shawnchain/aprs/doc/wiki/H618B_HOWTO/H618B.JPG

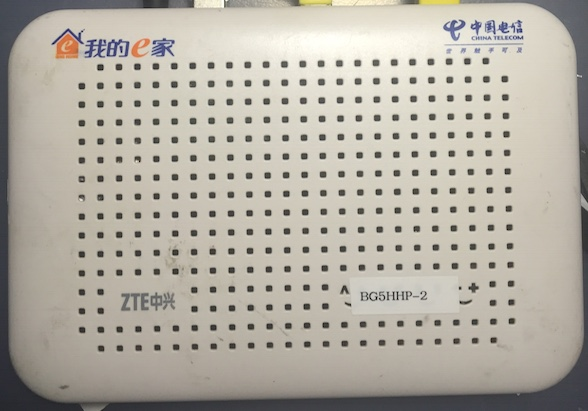
doc/wiki/H618B_HOWTO/H618B.JPG
