shawnchain/aprs/doc/wiki/H618B_HOWTO/H618B_SETUP_1.JPG

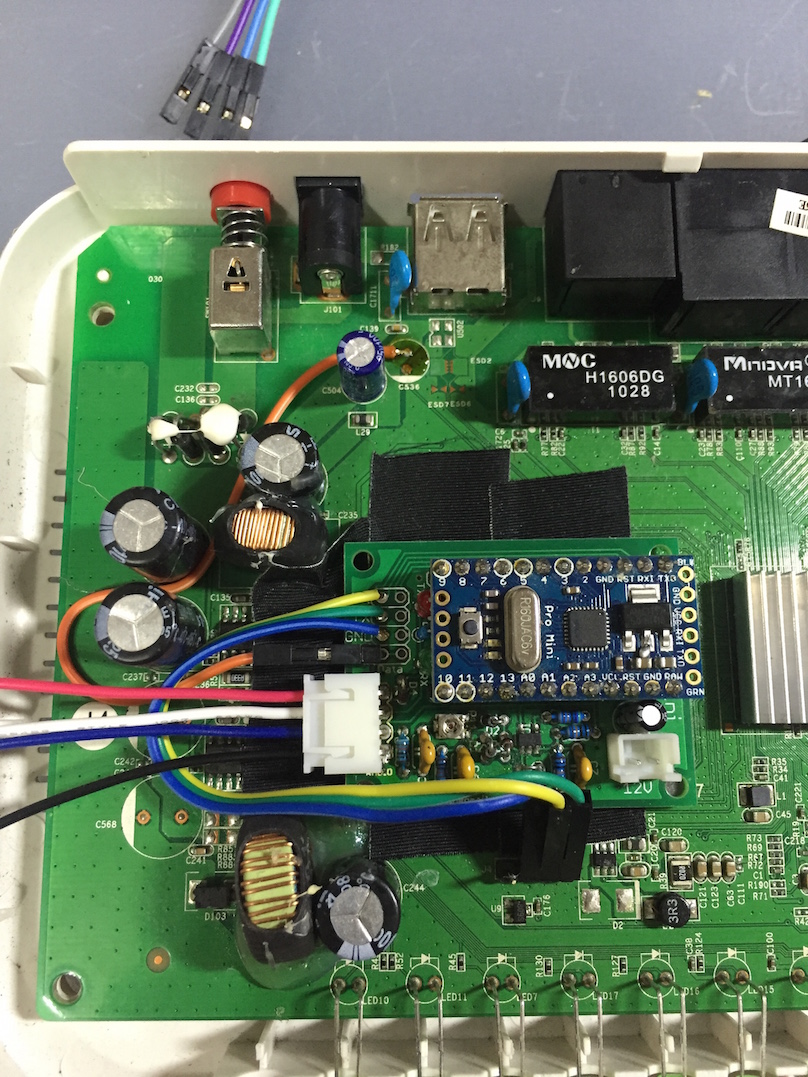
doc/wiki/H618B_HOWTO/H618B_SETUP_1.JPG
