shawnchain/aprs/doc/wiki/H618B_HOWTO/H618B_TTL.JPG

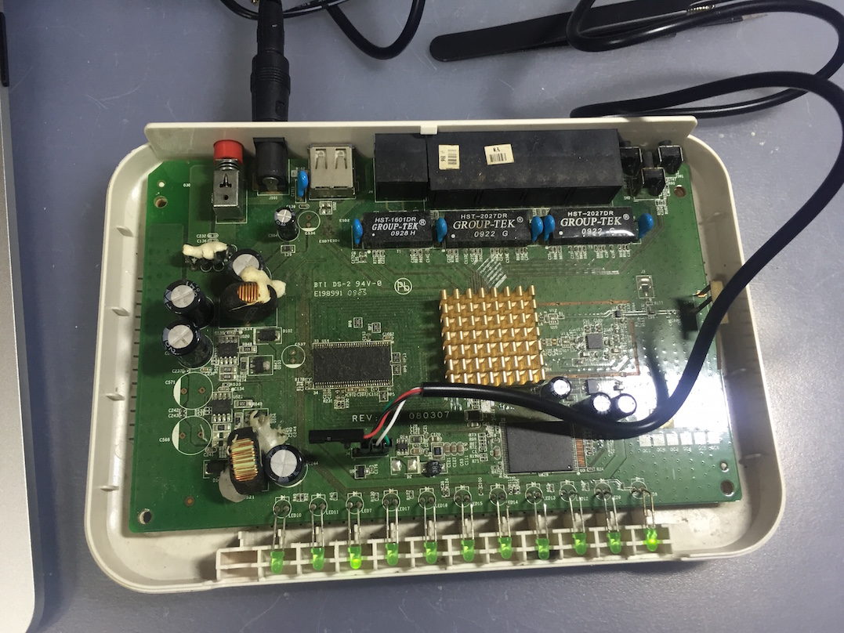
doc/wiki/H618B_HOWTO/H618B_TTL.JPG
