shawnchain/aprs/doc/wiki/SM50_HOWTO/pin_setup.JPG

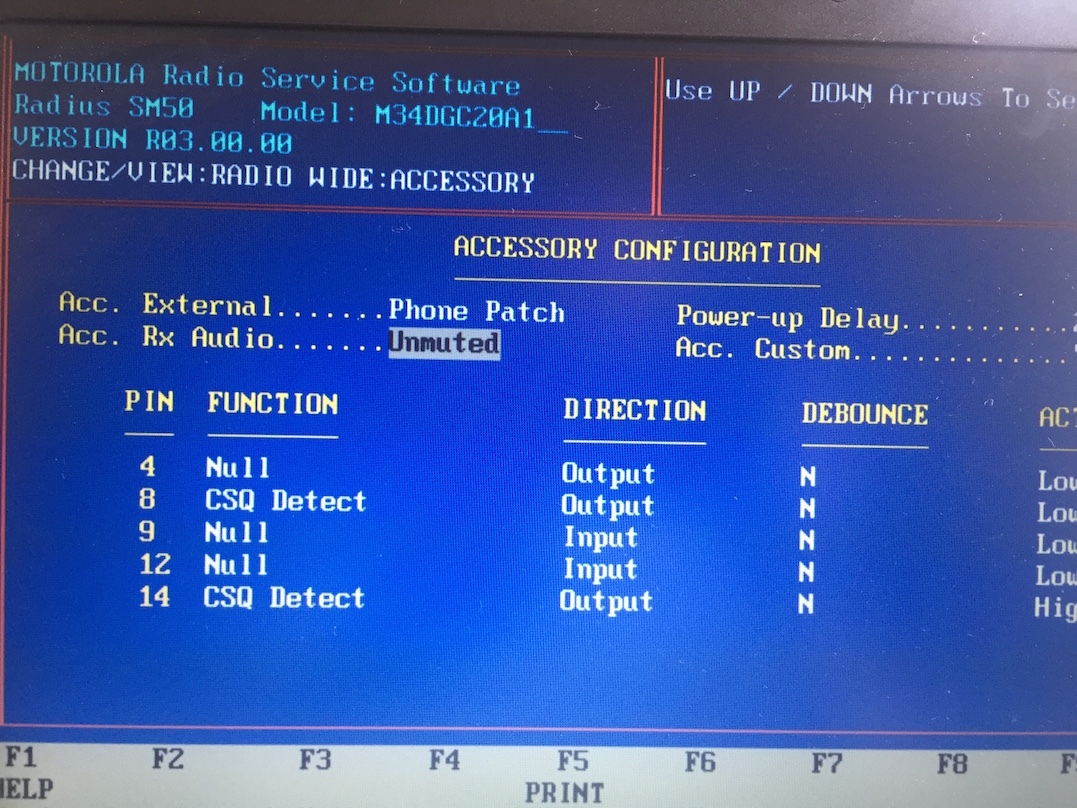
doc/wiki/SM50_HOWTO/pin_setup.JPG
