shawnchain/aprs/doc/wiki/SM50_HOWTO/setup_1.JPG

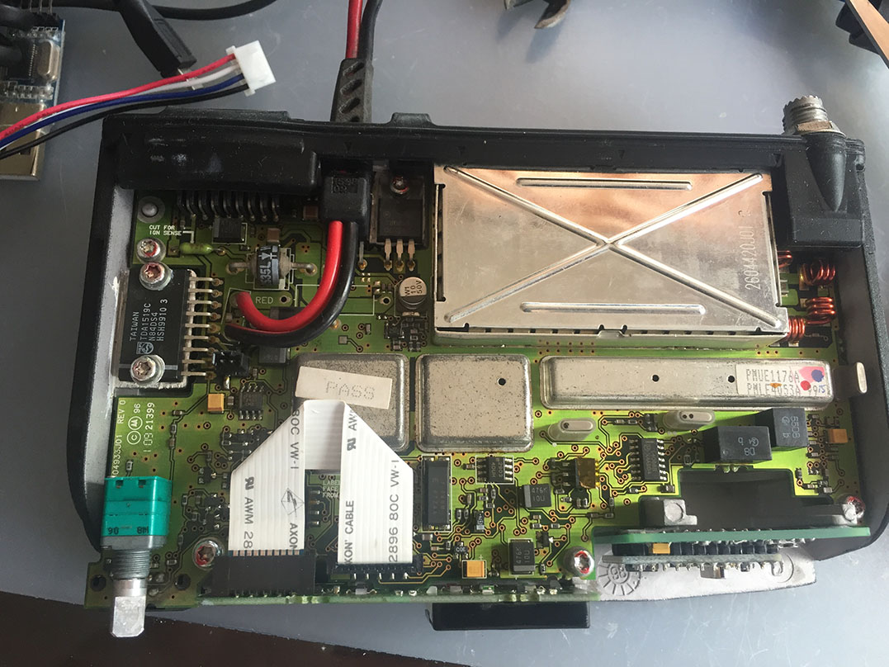
doc/wiki/SM50_HOWTO/setup_1.JPG
