shawnchain/aprs/doc/wiki/SM50_HOWTO/setup_2.JPG

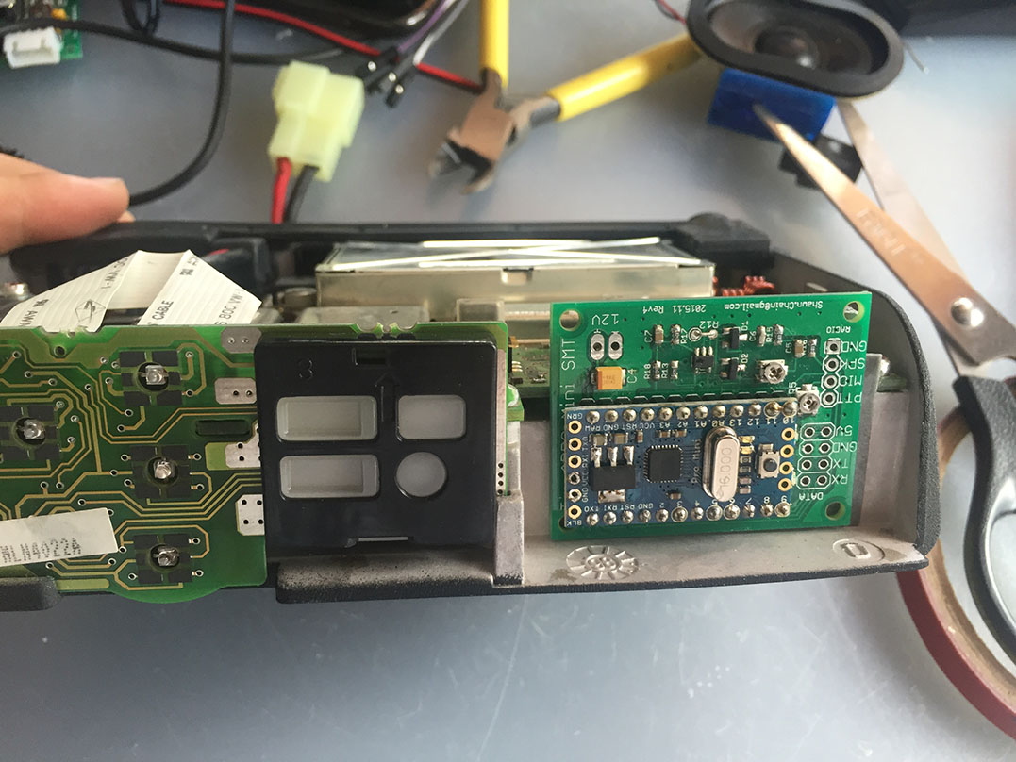
doc/wiki/SM50_HOWTO/setup_2.JPG
