shawnchain/aprs/doc/wiki/SM50_HOWTO/setup_4.JPG

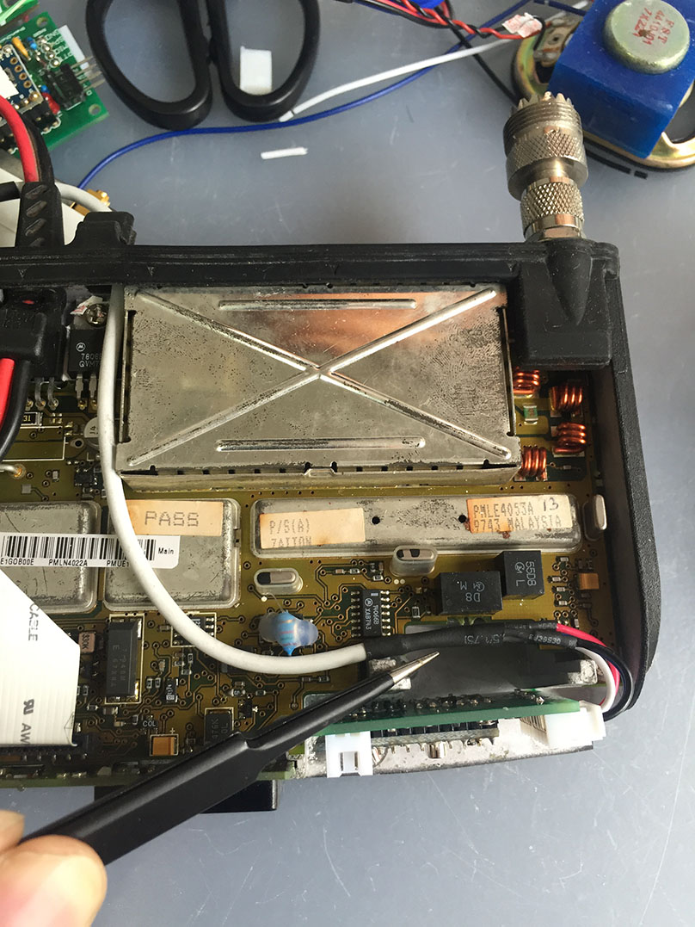
doc/wiki/SM50_HOWTO/setup_4.JPG
