shawnchain/aprs/doc/wiki/SM50_HOWTO/setup_5.JPG

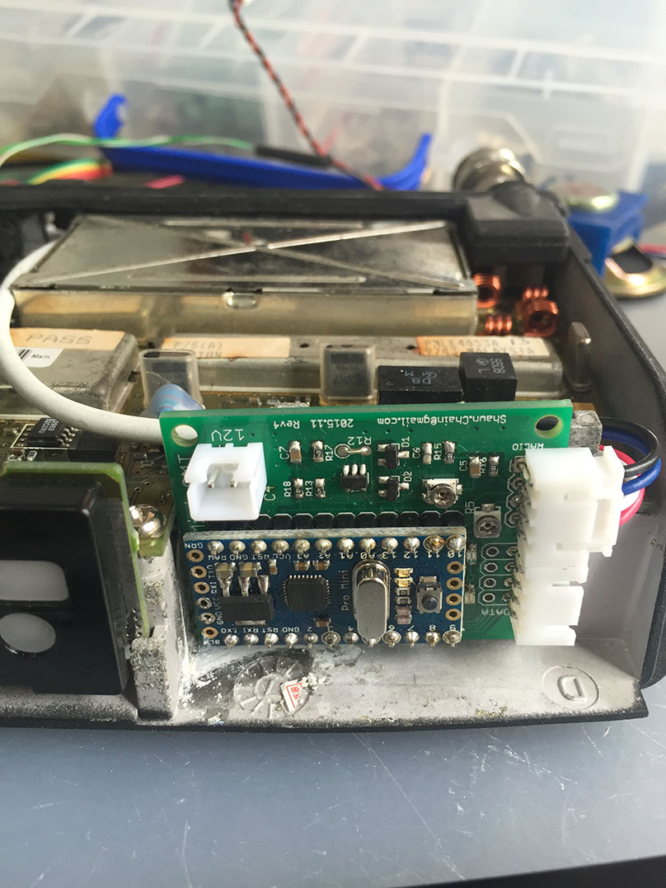
doc/wiki/SM50_HOWTO/setup_5.JPG
