shawnchain/aprs/doc/wiki/SM50_HOWTO/setup_6.JPG

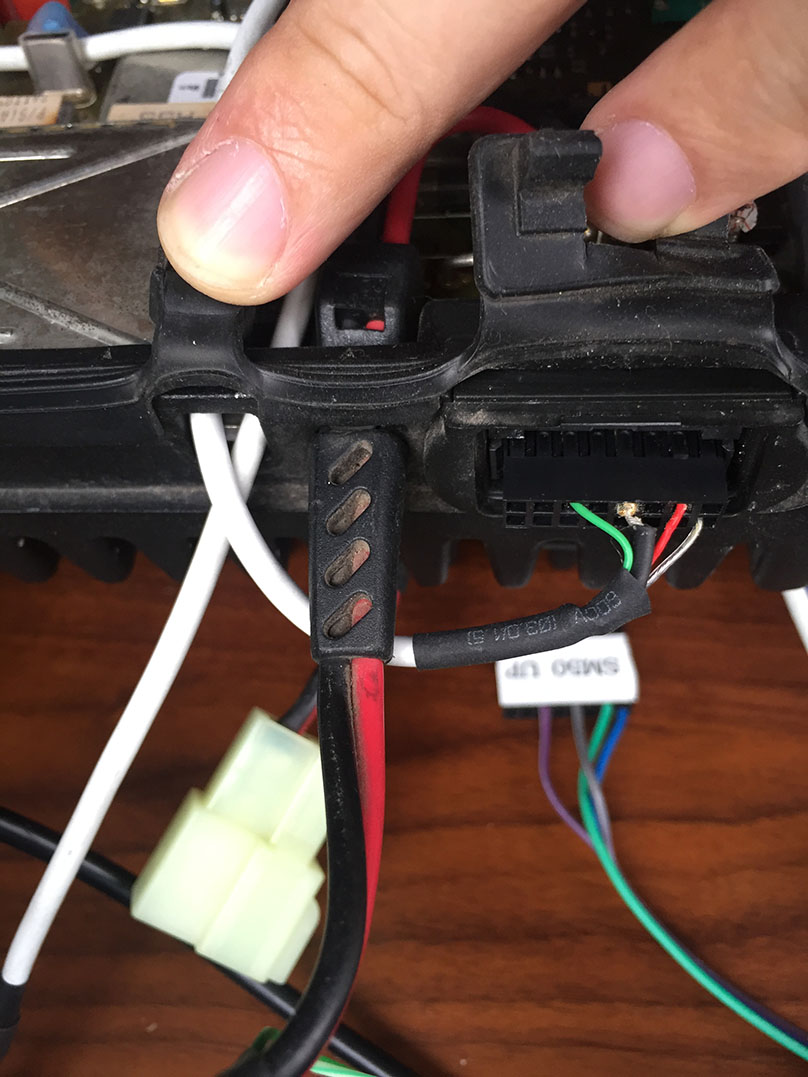
doc/wiki/SM50_HOWTO/setup_6.JPG
