shawnchain/aprs/doc/wiki/SM50_HOWTO/setup_7.JPG

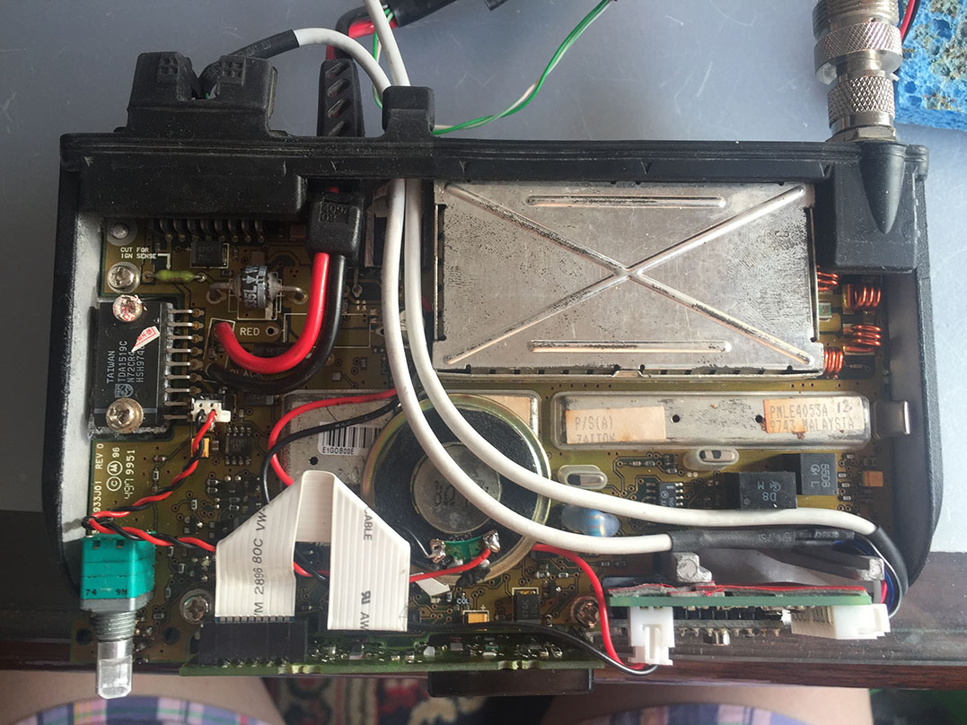
doc/wiki/SM50_HOWTO/setup_7.JPG
