shawnchain/aprs/doc/wiki/SM50_HOWTO/tx_setup_02.JPG

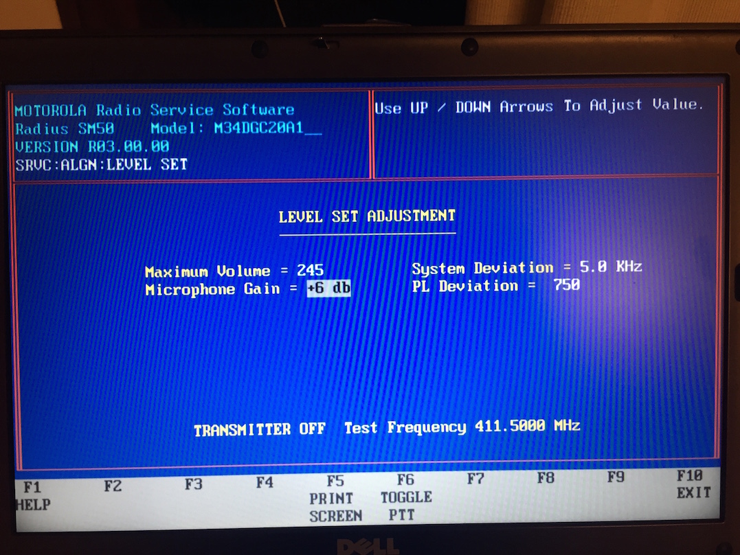
doc/wiki/SM50_HOWTO/tx_setup_02.JPG
