shawnchain/aprs/doc/wiki/SM50_HOWTO/tx_setup_03.JPG

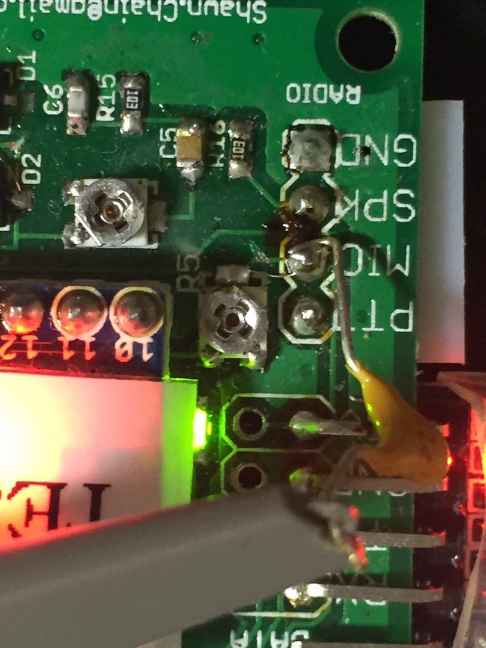
doc/wiki/SM50_HOWTO/tx_setup_03.JPG
