shawnchain/aprs/doc/wiki/SM50_HOWTO/tx_setup_04.JPG

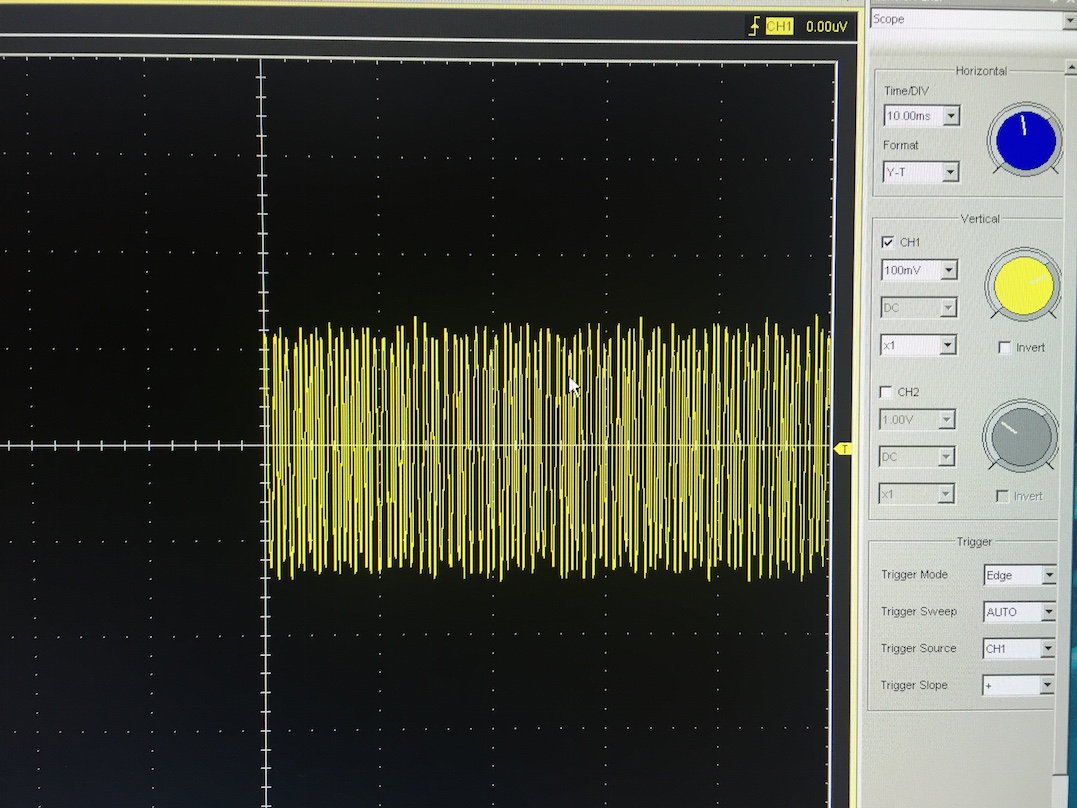
doc/wiki/SM50_HOWTO/tx_setup_04.JPG
