shawnchain/aprs/TinyAPRS/TinyAPRS/hw/hw_softser.c

#include <ctype.h>
#include <inttypes.h>
#include <avr/pgmspace.h>
#include <avr/interrupt.h>
#include <cfg/macros.h>
#include <cpu/irq.h>
#include <string.h>
#include <cfg/compiler.h>
#include "hw_softser.h"

#include "arduino_compat.h"

#if CFG_SOFTSER_RX_ENABLED
#define _SS_MAX_RX_BUFF CFG_SOFTSER_RXBUFSIZE // RX buffer size, see cfg_softser.h
static char _receive_buffer[_SS_MAX_RX_BUFF];
static volatile uint8_t _receive_buffer_tail = 0;
static volatile uint8_t _receive_buffer_head = 0;

SoftSerial *pActiveSerPort = NULL;

static void hw_softser_handle_interrupt(void);

#endif

//
// Lookup table
//
typedef struct _DELAY_TABLE {
	long baud;
	unsigned short rx_delay_centering;
	unsigned short rx_delay_intrabit;
	unsigned short rx_delay_stopbit;
	unsigned short tx_delay;
} DELAY_TABLE;

#if CPU_FREQ == 16000000 // defined in Makefile

static const DELAY_TABLE PROGMEM delayTable[] = {
//  baud, rxcenter, rxintra, rxstop, tx
	{115200, 1, 17, 17, 12,},
	{57600, 10, 37, 37, 33,},
	{38400, 25, 57, 57, 54,},
	{31250, 31, 70, 70, 68,},
	{28800, 34, 77, 77, 74,},
	{19200, 54, 117, 117, 114,},
	{14400, 74, 156, 156, 153,},
	{9600, 114, 236, 236, 233,},
	{4800, 233, 474, 474, 471,},
	{2400, 471, 950, 950, 947,},
	{1200, 947, 1902, 1902, 1899,},
	{600, 1902, 3804, 3804, 3800,},
	{300,3804, 7617, 7617, 7614,},
};

const int XMIT_START_ADJUSTMENT = 5;
#else

#error This version of SoftwareSerial supports only 16MHz processors

#endif

//
// Debugging
//
// This function generates a brief pulse
// for debugging or measuring on an oscilloscope.
INLINE void DebugPulse(uint8_t pin, uint8_t count) {
	(void) pin;
	(void) count;
	#if CFG_SOFTSER_DEBUG
	volatile uint8_t *pport = portOutputRegister(digitalPinToPort(pin));

	uint8_t val = *pport;
	while (count--)
	{
		*pport = val | digitalPinToBitMask(pin);
		*pport = val;
	}
	#endif
}

INLINE void hw_softser_tunedDelay(uint16_t delay) {
	uint8_t tmp = 0;
	asm volatile("sbiw    %0, 0x01 \n\t"
		"ldi %1, 0xFF \n\t"
		"cpi %A0, 0xFF \n\t"
		"cpc %B0, %1 \n\t"
		"brne .-10 \n\t"
		: "+r" (delay), "+a" (tmp)
		: "0" (delay)
	);
}

void hw_softser_init(SoftSerial *pSSer, uint8_t pinRX, uint8_t pinTX) {
	uint8_t port;
	memset(pSSer, 0, sizeof(SoftSerial));
	pSSer->_inverse_logic = false;
	(void)pinRX;(void)pinTX;
#if CFG_SOFTSER_TX_ENABLED
	pinMode(pinTX, OUTPUT);
	digitalWrite(pinTX, HIGH);
	pSSer->_transmitBitMask = digitalPinToBitMask(pinTX);
	port = digitalPinToPort(pinTX);
	pSSer->_transmitPortRegister = portOutputRegister(port);
#endif

#if CFG_SOFTSER_RX_ENABLED
	pinMode(pinRX, INPUT);
	if (!pSSer->_inverse_logic)
		digitalWrite(pinRX, HIGH);  // pullup for normal logic!
	pSSer->_receivePin = pinRX;
	pSSer->_receiveBitMask = digitalPinToBitMask(pinRX);
	port = digitalPinToPort(pinRX);
	pSSer->_receivePortRegister = portInputRegister(port);

	pActiveSerPort = pSSer;
#endif

}

void hw_softser_start(SoftSerial *pSSer, long speed) {
	// Enable the PinChangeInterrupt
	//	PCICR |= BV(PCIE2);
	//	PCMSK2 |= BV(PCINT18);// PORTD2 corresponding ISR mask is PCINT18
	for (unsigned i = 0; i < sizeof(delayTable) / sizeof(delayTable[0]); ++i) {
		long baud = pgm_read_dword(&delayTable[i].baud);
		if (baud == speed) {
			pSSer->_rx_delay_centering =
					pgm_read_word(&delayTable[i].rx_delay_centering);
			pSSer->_rx_delay_intrabit = pgm_read_word(&delayTable[i].rx_delay_intrabit);
			pSSer->_rx_delay_stopbit = pgm_read_word(&delayTable[i].rx_delay_stopbit);
			pSSer->_tx_delay = pgm_read_word(&delayTable[i].tx_delay);
			break;
		}
	}

#if CFG_SOFTSER_RX_ENABLED
	// Set up RX interrupts, but only if we have a valid RX baud rate
	uint8_t rPin = pSSer->_receivePin;

	if (pSSer->_rx_delay_stopbit) {
		/*
		 uint8_t *p = digitalPinToPCICR(rPin);
		 if (p > 0) {
		 *p |= _BV(digitalPinToPCICRbit(rPin));
		 (*digitalPinToPCMSK(rPin)) |= _BV(digitalPinToPCMSKbit(rPin));
		 }
		 */
		if (rPin <= 21) {
			PCICR |= _BV(digitalPinToPCICRbit(rPin));
			(*digitalPinToPCMSK(rPin)) |= _BV(digitalPinToPCMSKbit(rPin));
		}
		hw_softser_tunedDelay(pSSer->_tx_delay); // if we were low this establishes the end
	}

	#if CFG_SOFTSER_DEBUG
	pinMode(CFG_SOFTSER_DEBUG_PIN1, OUTPUT);
	pinMode(CFG_SOFTSER_DEBUG_PIN2, OUTPUT);
	#endif

	// Reset internal cache if incoming data is from another port that differs from the current one.
	if (pActiveSerPort != pSSer) {
		pSSer->_buffer_overflow = false;
		ATOMIC(_receive_buffer_head = 0; _receive_buffer_tail = 0; pActiveSerPort = pSSer;);
	}
#else
	(void)pSSer;(void)speed;
#endif
}

void hw_softser_stop(SoftSerial *pSSer) {
#if CFG_SOFTSER_RX_ENABLED
	/*
	 // Disable the PinChangeInterrupt
	 PCICR &= ~BV(PCIE2);
	 PCMSK2 &= ~BV(PCINT18);// PORTD2 corresponding ISR mask is PCINT18
	 */
	uint8_t rPin = pSSer->_receivePin;
	if (digitalPinToPCMSK(rPin)) {
		*digitalPinToPCMSK(rPin) &= ~_BV(digitalPinToPCMSKbit(rPin));
	}
#else
	(void)pSSer;
#endif
}

// Read data from buffer
int hw_softser_read(SoftSerial *pSSer) {
#if CFG_SOFTSER_RX_ENABLED
	if (pActiveSerPort != pSSer)
		return -1;

	// Empty buffer?
	if (_receive_buffer_head == _receive_buffer_tail)
		return -1;

	// Read from "head"
	uint8_t d = _receive_buffer[_receive_buffer_head]; // grab next byte
	_receive_buffer_head = (_receive_buffer_head + 1) % _SS_MAX_RX_BUFF;
	return d;
#else
	(void)pSSer;
	return -1;
#endif
}

int hw_softser_avail(SoftSerial *pSSer) {
#if CFG_SOFTSER_RX_ENABLED
	if (pActiveSerPort != pSSer) {
		return 0;
	}
	return (_receive_buffer_tail + _SS_MAX_RX_BUFF - _receive_buffer_head)
			% _SS_MAX_RX_BUFF;
#else
	(void)pSSer;
	return 0;
#endif
}

#define tx_pin_write(pSSer,pin_state) \
  if (pin_state == LOW){ \
	  *(pSSer->_transmitPortRegister) &= ~(pSSer->_transmitBitMask); \
  }else{ \
	  *(pSSer->_transmitPortRegister) |= pSSer->_transmitBitMask; \
  }

int hw_softser_write(SoftSerial *pSSer, uint8_t b) {
#if CFG_SOFTSER_TX_ENABLED
	if (pSSer->_tx_delay == 0) {
		return 0;
	}

	uint8_t oldSREG = SREG;
	cli();
	// turn off interrupts for a clean txmit

	// Write the start bit
	tx_pin_write(pSSer, pSSer->_inverse_logic ? HIGH : LOW);
	hw_softser_tunedDelay(pSSer->_tx_delay + XMIT_START_ADJUSTMENT);

	// Write each of the 8 bits
	bool HIGH_VALUE = pSSer->_inverse_logic?LOW:HIGH;
	bool LOW_VALUE = !HIGH_VALUE;
	for (uint8_t mask = 0x01; mask; mask <<= 1) {
		if (b & mask) { // choose bit
			tx_pin_write(pSSer, HIGH_VALUE); // send 1 ( or 0 in inverse logic)
		} else {
			tx_pin_write(pSSer, LOW_VALUE); // send 0 ( or 1 in inverse logic)
		}

		hw_softser_tunedDelay(pSSer->_tx_delay);
	}
	tx_pin_write(pSSer, HIGH_VALUE); // restore pin to natural state

	SREG = oldSREG; // turn interrupts back on
	hw_softser_tunedDelay(pSSer->_tx_delay);

	return 1;
#else
	(void)pSSer;(void)b;
	return 0;
#endif
}

int hw_softser_print(SoftSerial *pSSer, char* str){
#if CFG_SOFTSER_TX_ENABLED
	uint8_t i = 0;
	while(str[i] != 0 /*&& i < 255 */){
		hw_softser_write(pSSer,str[i]);
		i++;
	}
	return i;
#else
	(void)pSSer;(void)str;
	return 0;
#endif
}

#if CFG_SOFTSER_RX_ENABLED

#define rx_pin_read(pSSer) \
  (*(pSSer->_receivePortRegister) & (pSSer->_receiveBitMask))

//
// The receive routine called by the interrupt handler
//
static void hw_softser_recv(SoftSerial *pSSer) {

#if GCC_VERSION < 40302
	// Work-around for avr-gcc 4.3.0 OSX version bug
	// Preserve the registers that the compiler misses
	// (courtesy of Arduino forum user *etracer*)
	asm volatile(
		"push r18 \n\t"
		"push r19 \n\t"
		"push r20 \n\t"
		"push r21 \n\t"
		"push r22 \n\t"
		"push r23 \n\t"
		"push r26 \n\t"
		"push r27 \n\t"
		::);
#endif

	uint8_t d = 0;

	// If RX line is high, then we don't see any start bit
	// so interrupt is probably not for us
	if (pSSer->_inverse_logic ? rx_pin_read(pSSer) : !rx_pin_read(pSSer)) {
		// Wait approximately 1/2 of a bit width to "center" the sample
		hw_softser_tunedDelay(pSSer->_rx_delay_centering);
		DebugPulse(CFG_SOFTSER_DEBUG_PIN2, 1);

		// Read each of the 8 bits
		for (uint8_t i = 0x1; i; i <<= 1) {
			hw_softser_tunedDelay(pSSer->_rx_delay_intrabit);
			DebugPulse(CFG_SOFTSER_DEBUG_PIN2, 1);
			uint8_t noti = ~i;
			if (rx_pin_read(pSSer))
				d |= i;
			else
				// else clause added to ensure function timing is ~balanced
				d &= noti;
		}

		// skip the stop bit
		hw_softser_tunedDelay(pSSer->_rx_delay_stopbit);
		DebugPulse(CFG_SOFTSER_DEBUG_PIN2, 1);

		if (pSSer->_inverse_logic)
			d = ~d;

		// if buffer full, set the overflow flag and return
		if ((_receive_buffer_tail + 1) % _SS_MAX_RX_BUFF != _receive_buffer_head) {
			// save new data in buffer: tail points to where byte goes
			_receive_buffer[_receive_buffer_tail] = d; // save new byte
			_receive_buffer_tail = (_receive_buffer_tail + 1) % _SS_MAX_RX_BUFF;
		} else {
	#if CFG_SOFTSER_DEBUG // for scope: pulse pin as overflow indictator
			DebugPulse(CFG_SOFTSER_DEBUG_PIN1, 1);
	#endif
			pSSer->_buffer_overflow = true;
		}
	}

#if GCC_VERSION < 40302
// Work-around for avr-gcc 4.3.0 OSX version bug
// Restore the registers that the compiler misses
asm volatile(
		"pop r27 \n\t"
		"pop r26 \n\t"
		"pop r23 \n\t"
		"pop r22 \n\t"
		"pop r21 \n\t"
		"pop r20 \n\t"
		"pop r19 \n\t"
		"pop r18 \n\t"
		::);
#endif
}

INLINE void hw_softser_handle_interrupt() {
	if (pActiveSerPort) {
		hw_softser_recv(pActiveSerPort);
	}
}
 #if defined(PCINT0_vect)
 DECLARE_ISR(PCINT0_vect)
 {
	 hw_softser_handle_interrupt();
 }
 #endif

 #if defined(PCINT1_vect)
 DECLARE_ISR(PCINT1_vect)
 {
	 hw_softser_handle_interrupt();
 }
 #endif

#if defined(PCINT2_vect)
DECLARE_ISR(PCINT2_vect)
{
	hw_softser_handle_interrupt();
}
#endif

 #if defined(PCINT3_vect)
 DECLARE_ISR(PCINT3_vect)
 {
 hw_soft_ser_handle_interrupt();
 }
 #endif


#endif // end of #if CFG_SOFTSER_RX_ENABLED
