shawnchain/aprs/TinyAPRS/bertos/net/ax25.c

 /**
 * \file
 * <!--
 * This file is part of BeRTOS.
 *
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
 * As a special exception, you may use this file as part of a free software
 * library without restriction.  Specifically, if other files instantiate
 * templates or use macros or inline functions from this file, or you compile
 * this file and link it with other files to produce an executable, this
 * file does not by itself cause the resulting executable to be covered by
 * the GNU General Public License.  This exception does not however
 * invalidate any other reasons why the executable file might be covered by
 * the GNU General Public License.
 *
 * Copyright 2009 Develer S.r.l. (http://www.develer.com/)
 *
 * -->
 * \brief Simple AX25 data link layer implementation.
 *
 * For now, only UI frames without any Layer 3 protocol are handled.
 * This however is enough to send/receive APRS packets.
 *
 * \author Francesco Sacchi <batt@develer.com>
 *
 */

#include "ax25.h"
#include "cfg/cfg_ax25.h"

#include <algo/crc_ccitt.h>

#define LOG_LEVEL  AX25_LOG_LEVEL
#define LOG_FORMAT AX25_LOG_FORMAT
#include <cfg/log.h>

#include <string.h> //memset, memcmp
#include <ctype.h>  //isalnum, toupper

#include <cpu/pgm.h>
#include <stdio.h>

#include <cpu/irq.h>

/*
 * Decode the CALL field, assume addr is a fix-size array
 */
#define DECODE_CALL(buf, addr) \
	for (unsigned i = 0; i < sizeof((addr)); i++) \
	{ \
		char c = (*(buf)++ >> 1); \
		(addr)[i] = (c == ' ') ? '\x0' : c; \
	}

/*
 * The decoded ax25 frame contains:
 * | DST_ID(7) |SRC_ID(7) | RPT_LIST(7 * 8) | CTRL(0x03) | PID(0xF0) | PAYLOAD | LEN |
 */
static void ax25_decode(AX25Ctx *ctx)
{
	AX25Msg msg;
	uint8_t *buf = ctx->buf;

	DECODE_CALL(buf, msg.dst.call);
	msg.dst.ssid = (*buf++ >> 1) & 0x0F;

	DECODE_CALL(buf, msg.src.call);
	msg.src.ssid = (*buf >> 1) & 0x0F;

	LOG_INFO("SRC[%.6s-%d], DST[%.6s-%d]\n", msg.src.call, msg.src.ssid, msg.dst.call, msg.dst.ssid);

	/* Repeater addresses */
	#if CONFIG_AX25_RPT_LST
		for (msg.rpt_cnt = 0; !(*buf++ & 0x01) && (msg.rpt_cnt < countof(msg.rpt_lst)); msg.rpt_cnt++)
		{
			DECODE_CALL(buf, msg.rpt_lst[msg.rpt_cnt].call);
			msg.rpt_lst[msg.rpt_cnt].ssid = (*buf >> 1) & 0x0F;
			AX25_SET_REPEATED(&msg, msg.rpt_cnt, (*buf & 0x80));

			LOG_INFO("RPT%d[%.6s-%d]%c\n", msg.rpt_cnt, 
				msg.rpt_lst[msg.rpt_cnt].call, 
				msg.rpt_lst[msg.rpt_cnt].ssid,
				(AX25_REPEATED(&msg, msg.rpt_cnt) ? '*' : ' '));
		}
	#else
		while (!(*buf++ & 0x01))
		{
			char rpt[6];
			uint8_t ssid;
			DECODE_CALL(buf, rpt);
			ssid = (*buf >> 1) & 0x0F;
			LOG_INFO("RPT[%.6s-%d]\n", rpt, ssid);
		}
	#endif

	msg.ctrl = *buf++;
	if (msg.ctrl != AX25_CTRL_UI)
	{
		LOG_WARN("Only UI frames are handled, got [%02X]\n", msg.ctrl);
		return;
	}

	msg.pid = *buf++;
	if (msg.pid != AX25_PID_NOLAYER3)
	{
		LOG_WARN("Only frames without layer3 protocol are handled, got [%02X]\n", msg.pid);
		return;
	}

	msg.len = ctx->frm_len - 2 - (buf - ctx->buf);
	msg.info = buf;
	LOG_INFO("DATA: %.*s\n", msg.len, msg.info);

	if (ctx->hook)
		ctx->hook(&msg);
}


/**
 * Check if there are any AX25 messages to be processed.
 * This function read available characters from the medium and search for
 * any AX25 messages.
 * If a message is found it is decoded and the linked callback executed.
 * This function may be blocking if there are no available chars and the KFile
 * used in \a ctx to access the medium is configured in blocking mode.
 *
 * \param ctx AX25 context to operate on.
 */
void ax25_poll(AX25Ctx *ctx)
{
	int c;

	while ((c = kfile_getc(ctx->ch)) != EOF)
	{
		if (!ctx->escape && c == HDLC_FLAG)
		{
			if (ctx->frm_len >= AX25_MIN_FRAME_LEN)
			{
				if (ctx->crc_in == AX25_CRC_CORRECT)
				{
					LOG_INFO("Frame found!\n");
#if CONFIG_AX25_STAT
					ATOMIC(ctx->stat.rx_ok++);
#endif
					if (ctx->pass_through) {
						if (ctx->hook) {
							//TODO: make MSG union and pass to hook
							ctx->hook(NULL);
						}
					} else {
						ax25_decode(ctx);
					}
				}
				else
				{
					LOG_INFO("CRC error, computed [%04X]\n", ctx->crc_in);
#if CONFIG_AX25_STAT
					ATOMIC(ctx->stat.rx_err++);
#endif
				}
			}
			ctx->sync = true;
			ctx->crc_in = CRC_CCITT_INIT_VAL;
			ctx->frm_len = 0;

			ctx->dcd_state = 0;
			ctx->dcd = false;
			continue;
		}

		if (!ctx->escape && c == HDLC_RESET)
		{
			LOG_INFO("HDLC reset\n");
			ctx->sync = false;
			ctx->dcd = false;
			continue;
		}

		if (!ctx->escape && c == AX25_ESC)
		{
			ctx->escape = true;
			continue;
		}

		if (ctx->sync)
		{
			if (ctx->frm_len < CONFIG_AX25_FRAME_BUF_LEN)
			{
				ctx->buf[ctx->frm_len++] = c;
				ctx->crc_in = updcrc_ccitt(c, ctx->crc_in);

				if (ctx->dcd_state == 1 && c == AX25_PID_NOLAYER3) {
					ctx->dcd_state ++;
					ctx->dcd = true;
				}

				if (ctx->dcd_state == 0 && c == AX25_CTRL_UI) {
					ctx->dcd_state ++;
				}
			}
			else
			{
				LOG_INFO("Buffer overrun");
				ctx->sync = false;
				ctx->dcd = false;
#if CONFIG_AX25_STAT
				ATOMIC(ctx->stat.rx_err++);
#endif
			}
		}
		ctx->escape = false;
	}

	if (kfile_error(ctx->ch))
	{
		LOG_ERR("Channel error [%04x]\n", kfile_error(ctx->ch));
		kfile_clearerr(ctx->ch);
#if CONFIG_AX25_STAT
		if(ctx->dcd){
			ATOMIC(ctx->stat.rx_err++);
		}
#endif
		ctx->dcd = false;
	}
}

void ax25_putchar(AX25Ctx *ctx, uint8_t c)
{
	if (c == HDLC_FLAG || c == HDLC_RESET
		|| c == AX25_ESC)
		kfile_putc(AX25_ESC, ctx->ch);
	ctx->crc_out = updcrc_ccitt(c, ctx->crc_out);
	kfile_putc(c, ctx->ch);
}

static void ax25_sendCall(AX25Ctx *ctx, const AX25Call *addr, bool last,bool repeated)
{
	unsigned len = MIN(sizeof(addr->call), strlen(addr->call));

	for (unsigned i = 0; i < len; i++)
	{
		uint8_t c = addr->call[i];
		ASSERT(isalnum(c) || c == ' ');
		c = toupper(c);
		ax25_putchar(ctx, c << 1);
	}

	/* Fill with spaces the rest of the CALL if it's shorter */
	if (len < sizeof(addr->call))
		for (unsigned i = 0; i < sizeof(addr->call) - len; i++)
			ax25_putchar(ctx, ' ' << 1);

	/* The bit7 "has-been-repeated" flag is not implemented here */
	/* Bits6:5 should be set to 1 for all SSIDs (0x60) */
	/* The bit0 of last call SSID should be set to 1 */
	uint8_t ssid = 0x60 | (addr->ssid << 1) | (last ? 0x01 : 0);
	if(repeated) ssid |= 0x80;
	ax25_putchar(ctx, ssid);
}

/**
 * Send an AX25 frame on the channel through a specific path.
 * \param ctx AX25 context to operate on.
 * \param path An array of callsigns used as path, \see AX25_PATH for
 *        an handy way to create a path.
 * \param path_len callsigns path lenght.
 * \param _buf payload buffer.
 * \param len length of the payload.
 */
void ax25_sendVia(AX25Ctx *ctx, const AX25Call *path, size_t path_len, const void *_buf, size_t len)
{
	const uint8_t *buf = (const uint8_t *)_buf;
	ASSERT(path);
	ASSERT(path_len >= 2);

	ctx->crc_out = CRC_CCITT_INIT_VAL;
	kfile_putc(HDLC_FLAG, ctx->ch);


	/* Send call */
	for (size_t i = 0; i < path_len; i++)
		ax25_sendCall(ctx, &path[i], (i == path_len - 1), false /*repeated is not implemented*/);

	ax25_putchar(ctx, AX25_CTRL_UI);
	ax25_putchar(ctx, AX25_PID_NOLAYER3);

	while (len--)
		ax25_putchar(ctx, *buf++);

	/*
	 * According to AX25 protocol,
	 * CRC is sent in reverse order!
	 */
	uint8_t crcl = (ctx->crc_out & 0xff) ^ 0xff;
	uint8_t crch = (ctx->crc_out >> 8) ^ 0xff;
	ax25_putchar(ctx, crcl);
	ax25_putchar(ctx, crch);

	ASSERT(ctx->crc_out == AX25_CRC_CORRECT);

	// flush
	kfile_putc(HDLC_FLAG, ctx->ch);

#if CONFIG_AX25_STAT
	ATOMIC(ctx->stat.tx_ok++);
#endif
}

void ax25_sendMsg(AX25Ctx *ctx, const AX25Msg *msg){
	if(msg->rpt_cnt == 0 || msg->len == 0){
		return;
	}
	const uint8_t *buf = msg->info;
	size_t len = msg->len;

	ctx->crc_out = CRC_CCITT_INIT_VAL;
	kfile_putc(HDLC_FLAG, ctx->ch);

	// Send dest call
	ax25_sendCall(ctx, &(msg->dst), false, false);
	// send src call
	ax25_sendCall(ctx, &(msg->src), false, false);

	/* Send path calls */
	for (uint8_t i = 0; i < msg->rpt_cnt; i++){
		ax25_sendCall(ctx, msg->rpt_lst + i, (i == msg->rpt_cnt - 1),AX25_REPEATED(msg,i));
	}

	ax25_putchar(ctx, AX25_CTRL_UI);
	ax25_putchar(ctx, AX25_PID_NOLAYER3);

	while (len--)
		ax25_putchar(ctx, *buf++);

	/*
	 * According to AX25 protocol,
	 * CRC is sent in reverse order!
	 */
	uint8_t crcl = (ctx->crc_out & 0xff) ^ 0xff;
	uint8_t crch = (ctx->crc_out >> 8) ^ 0xff;
	ax25_putchar(ctx, crcl);
	ax25_putchar(ctx, crch);

	ASSERT(ctx->crc_out == AX25_CRC_CORRECT);

	kfile_putc(HDLC_FLAG, ctx->ch);

	// flush the channel, wait the radio send off
	kfile_flush(ctx->ch);

#if CONFIG_AX25_STAT
	ATOMIC(ctx->stat.tx_ok++);
#endif
}

void ax25_sendRaw(AX25Ctx *ctx, const void *_buf, size_t len)
{
	const uint8_t *buf = (const uint8_t *)_buf;

	ctx->crc_out = CRC_CCITT_INIT_VAL;
	kfile_putc(HDLC_FLAG, ctx->ch);

	while (len--)
		ax25_putchar(ctx, *buf++);

	/*
	 * According to AX25 protocol,
	 * CRC is sent in reverse order!
	 */
	uint8_t crcl = (ctx->crc_out & 0xff) ^ 0xff;
	uint8_t crch = (ctx->crc_out >> 8) ^ 0xff;
	ax25_putchar(ctx, crcl);
	ax25_putchar(ctx, crch);

	ASSERT(ctx->crc_out == AX25_CRC_CORRECT);

	kfile_putc(HDLC_FLAG, ctx->ch);

	// flush the channel, wait the radio send off
	kfile_flush(ctx->ch);

#if CONFIG_AX25_STAT
	ATOMIC(ctx->stat.tx_ok++);
#endif
}

static void print_call(KFile *ch, const AX25Call *call)
{
#if CPU_AVR
	kfile_printf_P(ch, PSTR("%.6s"), call->call);
	if (call->ssid)
		kfile_printf_P(ch, PSTR("-%d"), call->ssid);
#else
	kfile_printf(ch, "%.6s", call->call);
	if (call->ssid)
		kfile_printf(ch, "-%d", call->ssid);
#endif
}

/**
 * Print a AX25 message in TNC-2 packet monitor format.
 * \param ch a kfile channel where the message will be printed.
 * \param msg the message to be printed.
 */
void ax25_print(KFile *ch, const AX25Msg *msg)
{
	print_call(ch, &msg->src);
	kfile_putc('>', ch);
	print_call(ch, &msg->dst);

	#if CONFIG_AX25_RPT_LST
	for (int i = 0; i < msg->rpt_cnt; i++)
	{
		kfile_putc(',', ch);
		print_call(ch, &msg->rpt_lst[i]);
		/* Print a '*' if packet has already been transmitted 
		 * by this repeater */
		if (AX25_REPEATED(msg, i))
			kfile_putc('*', ch);
	}
	#endif

#if CPU_AVR
	kfile_printf_P(ch, PSTR(":%.*s\n\r"), msg->len, msg->info);
#else
	kfile_printf_P(ch, ":%.*s\n\r", msg->len, msg->info);
#endif
}


/**
 * Init the AX25 protocol decoder.
 *
 * \param ctx AX25 context to init.
 * \param channel Used to gain access to the physical medium
 * \param hook Callback function called when a message is received
 */
void ax25_init(AX25Ctx *ctx, KFile *channel, ax25_callback_t hook)
{
	ASSERT(ctx);
	ASSERT(channel);

	memset(ctx, 0, sizeof(*ctx));
	ctx->ch = channel;
	ctx->hook = hook;
	// decode the AX.25 frame needs extra memory but necessary acting as digipeater
	// or for displaying/debug purpose.
	// AS a TNC modem with KISS protocol used, pass_though could be enabled(set=1)
	ctx->pass_through = 0;
	ctx->crc_in = ctx->crc_out = CRC_CCITT_INIT_VAL;
}
