shawnchain/aprs/TinyAPRS/bertos/drv/ow_ds2438.c

/**
 * \file
 * <!--
 * This file is part of BeRTOS.
 *
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
 *  Copyright (C) 2012 Robin Gilks
 * -->
 *
 * \brief Driver for Dallas battery monitor  1-wire device
 *
 * \author Robin Gilks <g8ecj@gilks.org>
 */

#include "ow_ds2438.h"
#include "cfg/cfg_1wire.h"
#include "drv/ow_1wire.h"

#define LOG_LEVEL   OW_LOG_LEVEL
#define LOG_FORMAT  OW_LOG_FORMAT

#include <cfg/log.h>

#include <algo/crc8.h>
#include <drv/timer.h>
#include <stdbool.h>
#include <stdlib.h>





// values used to track battery charge when ICA doesn't have enough range
#define ICAREF    120
#define ICABAND    20

static int ow_ds2438_setICA(uint8_t id[], uint8_t value);


/**
 * Reads a page of EEPROM/SRAM via the scratchpad
 * \param id       the serial number for the part that the read is to be done on.
 * \param page_num page number to read fromn the 2438
 * \param rec_buf  8 byte (minimum) buffer for the page contents
 *
 * \return true if all OK else return false
 */

static int
ReadPage(uint8_t id[], int page_num, uint8_t * rec_buf)
{
	uint8_t read_block[10];
	int cnt = 0;
	uint8_t crc;

	// Recall page command
	ow_command(0xB8, id);
	// Page to Recall
	ow_byte_wr(page_num);

	// Read scratchpad command
	ow_command(0xBE, id);
	// Page to read
	ow_byte_wr(page_num);

	for (cnt = 0; cnt < 9; cnt++)
		read_block[cnt] = ow_byte_rd();

	crc = crc8(read_block, 9);
	if (crc != 0x00)
		return false;

	for (cnt = 0; cnt < 8; cnt++)
		rec_buf[cnt] = read_block[cnt];

	return true;
}

/**
 * Writes a page of EEPROM/SRAM via the scratchpad
 *          assumes the serial num has already been set
 * \param id       the serial number for the part that the read is to be done on.
 * \param page_num page number to write to the 2438
 * \param tx_buf   buffer of the page contents
 * \param tx_len   length of data to be written (need not be a full page)
 *
 * \return true if all OK else return false
 */

static int
WritePage(uint8_t id[], int page_num, uint8_t * tx_buf, int tx_len)
{
	uint8_t busybyte;

	// Write scratchpad command
	ow_command(0x4E, id);

	// Write page
	ow_byte_wr(page_num);
	ow_block(tx_buf, tx_len);

	// Copy scratchpad command
	ow_command(0x48, id);

	// Copy page
	ow_byte_wr(page_num);
	busybyte = ow_byte_rd();

	while (busybyte == 0)
		busybyte = ow_byte_rd();

	return true;
}

/**
 * Sets the DS2438 configuration register and initialises the charge variables
 *
 * \param id       the serial number for the part that the read is to be done on.
 * \param config   value to write to the config register to set the mode
 *
 * \return 'true' if the read was complete
 */

int
ow_ds2438_setup(uint8_t id[], int config)
{
	uint8_t send_block[10];

	// Get the Status/Configuration page
	if (!ReadPage(id, 0, send_block))
		return false;

	// if there is no change required in the config register, then leave it alone
	if ((send_block[0] & CONF2438_ALL) == config)
		return true;

	// set config byte
	send_block[0] = config;
	if (WritePage(id, 0, send_block, 1))
		return true;

	return false;
}

/**
 * Sets the internal 16 bit fake ICA register from the amp-hr charge value.
 * Also saves the shunt resistor value in the context so we don't have to keep passing it round.
 *
 * \param id       the serial number for the part that the read is to be done on.
 * \param context  pointer to the context for this device. 
 * \param shunt    the value of the current measuring shunt resistor in ohms
 * \param charge   initial charge in the battery (we then track it)
 *
 * \return true if all OK else return false
 */

int
ow_ds2438_init(uint8_t id[], CTX2438_t * context, float shunt, uint16_t charge)
{
	context->shunt = shunt;
	context->Charge = charge;

	if (!ow_ds2438_setup(id, CONF2438_IAD | CONF2438_CA | CONF2438_EE))
		return false;
	// initialise the ICA register to the middle of its range
	if (!ow_ds2438_setICA(id, ICAREF))
		return false;

	context->lastICA = ICAREF;
	context->fullICA = charge * 2048.0 * shunt * 100;

	return true;

}


/**
 * Sets the DS2438 to trigger all readable values
 * \note This function blocks until the conversions are complete
 *
 * \param id       the serial number for the part that the read is to be done on.
 */

void
ow_ds2438_doconvert(uint8_t id[])
{
	uint8_t busybyte;

	// start temperature conversion
	ow_command(0x44, id);
	busybyte = ow_byte_rd();
	while (busybyte == 0)
		busybyte = ow_byte_rd();

	// start voltage conversion
	ow_command(0xB4, id);
	busybyte = ow_byte_rd();
	while (busybyte == 0)
		busybyte = ow_byte_rd();

}

/**
 * Sets the DS2438 to read all values
 * the ICA register, being only 8 bits wide, is not big enough to cover the charge
 * range of a large battery bank. For this reason we take the changes that
 * occur in it and use them to adjust a 16 bit variable. We keep the ICA register
 * in the centre of its range to avoid overflow.
 * We keep a copy of our 16bit pseudo ICA register in EEPROM so it is non-volatile
 *
 * \param id       the serial number for the part that the read is to be done on.
 * \param context  context pointer to a structure of results
 *
 * \return 'true' if the read was complete
 */

int
ow_ds2438_readall(uint8_t id[], CTX2438_t * context)
{
	uint8_t page_data[10];
	int32_t lt;
	uint8_t ICA;

	if (!ReadPage(id, 0, page_data))
		return false;

	lt = (page_data[2] << 8) | page_data[1];
	// Scale up by 100 to keep the following arithmetic as integer. Note we have to go to 32 bits here!
	lt *= 100L;
	// now for a bit of magic!
	// There are 8 bits to 1 deg but the 38 has 12 bits but the 3 LSBs are not used 
	// so shift by 8 to scale the value and get the resolution to the correct place
	context->Temp = lt >> 8;

	// voltage can only be positive!! 10mV resolution gives us 2 decimal places
	context->Volts = ((page_data[4] << 8) | page_data[3]);

	// This is the voltage across the shunt resistor in units of 0.2441mV
	lt = page_data[6] << 8 | page_data[5];
	// We get passed the shunt resistor value as we're the only ones who know what the algorithm is
	// for calculating amps from the measured value.
	context->Amps = lt * 100 / (4096 * context->shunt);

	if (!ReadPage(id, 1, page_data))
		return false;

	// elapsed time meter register. 
	context->etm =                     page_data[3];
	context->etm = context->etm << 8 | page_data[2];
	context->etm = context->etm << 8 | page_data[1];
	context->etm = context->etm << 8 | page_data[0];

	ICA = page_data[4];

	if (!ReadPage(id, 7, page_data))
		return false;
	context->CCA = ((page_data[5] << 8) | page_data[4]) / (64.0 * context->shunt);
	context->DCA = ((page_data[7] << 8) | page_data[6]) / (64.0 * context->shunt);

	// a miss-read would likely return more than a change of 1 so only allow 2 or less
	// Note that the internal ICA value is scaled up by 100 so we don't loose accuracy on small adjustments due to charge inefficiency
	if (abs(ICA - context->lastICA) <= 2)
	{
		context->fullICA += (ICA - context->lastICA) * 100;
		context->lastICA = ICA;
		if ((ICA <= ICAREF - ICABAND) || (ICA >= ICAREF + ICABAND))
		{
			// if discharging and charge/discharge ratio < 1 then adjust ICA down by the efficiency of the charge cycle
			// this extra check is required because on a new system the recorded values of DCA and CCA are of the same magnitude as a normal discharge cycle
			if ((ICA <= ICAREF - ICABAND) && (context->DCA < context->CCA))
			{
				lt = context->fullICA;
				context->fullICA -= ICABAND * 100 * (1.0 - ((float) context->DCA / context->CCA));
				LOG_INFO("Adjusting local ICA (%ld), to %lu\r\n", lt, context->fullICA);
			}

			context->lastICA = ICAREF;
			ow_ds2438_setICA(id, ICAREF);
		}
	}
	else
	{
		LOG_INFO("Bad ICA read of %u, expecting closer to %u\r\n", ICA, context->lastICA);
	}

	context->Charge = (context->fullICA /  (2048.0 * context->shunt * 100)) + 0.5;

	return true;
}


/**
 * Sets the offset register and clears the threshold
 * \param id       the serial number for the part that the read is to be done on.
 * \param context  context pointer to a structure of results
 * \param offset   does automatic zeroing according to spec sheet and then adds the current offset supplied
 *
 * \return true if all OK else return false
 */

int
ow_ds2438_calibrate(uint8_t id[], CTX2438_t * context, int16_t offset)
{

	uint8_t rec_block[10];
	uint8_t config;
	int16_t regval;


	// Get the Status/Configuration page
	if (!ReadPage(id, 0, rec_block))
		return false;

	// save the config for when we have done
	config = rec_block[0];

	// turn off current sensing
	ow_ds2438_setup(id, 0);
	// wait for the ADC to stop
	timer_delay(40);

	// Get offset register from page 1
	if (!ReadPage(id, 1, rec_block))
		return false;

	// clear the offset reg
	rec_block[5] = 0;
	rec_block[6] = 0;

	// Write the page back
	if (!WritePage(id, 1, rec_block, 8))
		return false;

	ow_ds2438_setup(id, CONF2438_IAD);
	// wait for the ADC to start
	timer_delay(40);
	// Get Current register - it should read zero from page 0
	if (!ReadPage(id, 0, rec_block))
		return false;

	// turn off current sensing
	ow_ds2438_setup(id, 0);
	// wait for the ADC to stop
	timer_delay(40);

	regval = (rec_block[6] << 8) | rec_block[5];
	// get a clean copy of what is in page 1
	if (!ReadPage(id, 1, rec_block))
		return false;

	// offset comes to us in Amps * 100. Convert to 0.2441mV units and account for the 3 bit shift in the register
	offset = offset * (float) (4096.0 * context->shunt * 8.0 / 100.0) + 0.5;

	regval = (0 - regval) << 3;
	regval += offset;
	rec_block[5] = regval & 0xff;
	rec_block[6] = regval >> 8;

	// Write the page back
	if (!WritePage(id, 1, rec_block, 8))
		return false;

	return (ow_ds2438_setup(id, config));

}

/**
 * Sets the ICA register
 * \param id       the serial number for the part that the read is to be done on.
 * \param value    what to write to the ICA register
 *
 * \return true if all OK else return false
 */
static int
ow_ds2438_setICA(uint8_t id[], uint8_t value)
{
	uint8_t page_data[10];

	// Get ICA register from page 1
	if (!ReadPage(id, 1, page_data))
		return false;

	// slip in the new value
	page_data[4] = value;

	// Write the page back
	if (!WritePage(id, 1, page_data, 8))
		return false;

	return true;

}


/**
 * Sets the ETM register
 * \param id       the serial number for the part that the read is to be done on.
 * \param value    what to write to the ETM register
 *
 * \return true if all OK else return false
 */
int
ow_ds2438_setETM(uint8_t id[], uint32_t value)
{
	uint8_t page_data[10];

	// Get page 1
	if (!ReadPage(id, 1, page_data))
		return false;

	// slip in the new value
	page_data[0] = value & 0xff;
	page_data[1] = value >> 8;
	page_data[2] = value >> 16;
	page_data[3] = value >> 24;

	// Write the page back
	if (!WritePage(id, 1, page_data, 8))
		return false;

	return true;

}



/**
 * Sets the CCA and DCA registers
 * \param id       the serial number for the part that the read is to be done on.
 * \param context  context pointer that contains the DCA and CCA values in amp-hrs to be written 
 *
 * \return true if all OK else return false
 */
int
ow_ds2438_setCCADCA(uint8_t id[], CTX2438_t * context)
{
	uint8_t page_data[10];
	int32_t cca, dca;

	cca = context->CCA * (float) (64.0 * context->shunt);
	dca = context->DCA * (float) (64.0 * context->shunt);


	// Get registers from page 7
	if (!ReadPage(id, 7, page_data))
		return false;

	// do the CCA/DCA regs
	if (cca >= 0)
	{
		page_data[4] = cca & 0xff;
		page_data[5] = (cca >> 8) & 0xff;
	}
	if (dca >= 0)
	{
		page_data[6] = dca & 0xff;
		page_data[7] = (dca >> 8) & 0xff;
	}

	// Write the page back
	if (!WritePage(id, 7, page_data, 8))
		return false;

	return true;
}
