shawnchain/aprs/TinyAPRS/TinyAPRS/lcd/hw_lcd_4884.c

#include "hw_lcd_4884.h"

#include <net/afsk.h>
#include <cpu/irq.h>

#include <avr/io.h>
#include <avr/interrupt.h>
#include <avr/pgmspace.h>

#include <drv/timer.h>

static void hw_lcd_4884_send(uint8_t type, uint8_t data);

/*
 * TODO - PIN Configuration for Microduino 644PA
 *
 *
 */
#if defined(MICRODUINO_644PA) && (MICRODUINO_644PA == 1)

#define HW_LCD_INIT() do { DDRB |= BV(1)|BV(2);/*PIN9, PIN10*/ } while (0)
#define HW_LCD_SCLK_ON()   do { PORTB |= BV(1); } while (0)
#define HW_LCD_SCLK_OFF()  do { PORTB &= ~BV(1); } while (0)

#else

/*
 * PIN Configuration for Microduino 328P
 *
 * PORTC(1)/D15/A1 -> CLK
 * PORTC(2)/D16/A2 -> DIN
 * PORTC(3)/D17/A3 -> DC
 * PORTC(4)/D18/A4 -> SCE
 * PORTC(5)/D19/A5 -> RST
 *
 * value = 62(00111110) (BV(PIN_SCLK)|BV(PIN_SDIN)|BV(PIN_DC)|BV(PIN_RESET)|BV(PIN_SCE));
 */
//
#define HW_LCD_INIT() do { DDRC |= BV(1)|BV(2)|BV(3)|BV(4)|BV(5); PORTC |= BV(1)|BV(2)|BV(3)|BV(4)|BV(5);} while (0)

#define HW_LCD_SCLK_HI()	do { PORTC |= BV(1); } while (0)
#define HW_LCD_SCLK_LO()	do { PORTC &= ~BV(1); } while (0)

#define HW_LCD_SDIN_HI()	do { PORTC |= BV(2); } while (0)
#define HW_LCD_SDIN_LO()	do { PORTC &= ~BV(2); } while (0)

#define HW_LCD_DC_HI()		do { PORTC |= BV(3); } while (0)
#define HW_LCD_DC_LO()		do { PORTC &= ~BV(3); } while (0)

#define HW_LCD_SCE_HI()		do { PORTC |= BV(4); } while (0)
#define HW_LCD_SCE_LO()	do { PORTC &= ~BV(4); } while (0)

#define HW_LCD_RESET_HI()	do { PORTC |= BV(5); } while (0)
#define HW_LCD_RESET_LO()	do { PORTC &= ~BV(5); } while (0)

#define HW_LCD_PIN_HI(x)	do { PORTC |= BV(x); } while (0)
#define HW_LCD_PIN_LO(x)	do { PORTC &= ~BV(x); } while (0)
#endif

#define PIN_SCLK 1
#define PIN_SDIN 2
#define PIN_DC 3
#define PIN_SCE 4
#define PIN_RESET 5

#define HI(x) PORTC |= BV(x)
#define LO(x) PORTC &= ~BV(x)


#define PCD8544_CMD  0
#define PCD8544_DATA 1
#define HW_LCD_CMD(x) hw_lcd_4884_send(PCD8544_CMD,x)
#define HW_LCD_DATA(x) hw_lcd_4884_send(PCD8544_DATA,x)
///////////////////////////////////////////////
// Internal variables
///////////////////////////////////////////////
// The size of the display, in pixels...
#define width 84
#define height 48

#define NUM_COL 14
#define NUM_ROW 5

// Current cursor position...
static unsigned char pix_x;
static unsigned char pix_y;

///////////////////////////////////////////////
// Internal functions
///////////////////////////////////////////////


///////////////////////////////////////////////
// Public functions
///////////////////////////////////////////////
void lcd_4884_init(){
	HW_LCD_INIT();
#if 0
	for(uint16_t i = 0;i < 1000;i++){
		if(i % 2 == 0)
			HI(PIN_SCLK);
			//PORTC |= 62;
		else{
			//PORTC &= ~62;
			LO(PIN_SCLK);
		}
		timer_delay(1000);
	}
#else
	// reset the controller
	HW_LCD_RESET_HI();
	timer_delay(1);
	HW_LCD_RESET_LO();
	timer_delay(1);
	HW_LCD_RESET_HI();
	timer_delay(100);

	/*
	LO(PIN_SCE);
	timer_delay(1);
	HI(PIN_SCE);
	*/

	// set parameters
	HW_LCD_CMD(0x21); // extended instruction set control (H=1)
	HW_LCD_CMD(0xc0); // bias system (1:48)

	HW_LCD_CMD(0x06);
	HW_LCD_CMD(0x13);
	HW_LCD_CMD(0x20); // set enable

	lcd_4884_clear();
	HW_LCD_CMD(0x0c); // normal mode(0x0d = inverse mode)

	// all done, keep low of PIN_SCE
	HW_LCD_SCE_LO();

	/*
#if defined(CHIP_ST7576) && CHIP_ST7576 == 1
	hw_lcd_4884_send(PCD8544_CMD,0xe0);
	hw_lcd_4884_send(PCD8544_CMD,0x05);
#else
	hw_lcd_4884_send(PCD8544_CMD,0xc2);
#endif
	hw_lcd_4884_send(PCD8544_CMD,0x20);
	hw_lcd_4884_send(PCD8544_CMD,0x09);

	// clear the ram
	lcd_4884_clear();

	hw_lcd_4884_send(PCD8544_CMD,0x08); //display blank
	hw_lcd_4884_send(PCD8544_CMD,0x0c); // normal mode(0x0d = inverse mode)
	timer_delay(100);

	// reset cursor
	hw_lcd_4884_send(PCD8544_CMD,0x80);
	hw_lcd_4884_send(PCD8544_CMD,0x40);
	*/
#endif
}

static void hw_lcd_4884_send(uint8_t type, uint8_t data){
	uint8_t i;

	HW_LCD_SCE_LO();
	if(type ==  0){
		// this is command
		HW_LCD_DC_LO();
	}else{
		// this is data
		HW_LCD_DC_HI();
	}

	// shift data out
	for (i = 0; i < 8; i++) {
		if((data & (1 << (7 - i)))){
			HW_LCD_SDIN_HI();
		}else{
			HW_LCD_SDIN_LO();
		}
		HW_LCD_SCLK_LO();
		HW_LCD_SCLK_HI();
		/*
		if(data& 0x80) {
			HW_LCD_SDIN_HI();
		} else {
			HW_LCD_SDIN_LO();
		}
		HW_LCD_SCLK_LO();
		data = data << 1;
		HW_LCD_SCLK_HI();
		*/
	}

	HW_LCD_SCE_HI();
}

void lcd_4884_home(){
	lcd_4884_setCursor(0,pix_y);
}

void lcd_4884_setCursor(uint8_t x, uint8_t y){
	pix_x = x % width;
	pix_y = y % height;
	HW_LCD_CMD(0x80 | pix_x);
	HW_LCD_CMD(0x40 | pix_y);
}


void lcd_4884_clear() {
	lcd_4884_setCursor(0, 0);
	// the font 6x8 is 6 pix width and 8 pix height
	for (uint16_t i = 0; i < width * (height / 8) /*504*/; i++) {
		HW_LCD_DATA(0x00);
	}
	lcd_4884_setCursor(0, 0);
}

void lcd_4884_clearLine(uint8_t aline){
	lcd_4884_setCursor(0, aline);
	for (uint16_t i = 0; i < width; i++) {
		HW_LCD_DATA(0x00);
	}
	lcd_4884_setCursor(0, aline);
}

void lcd_4884_writeString(const char* str,uint8_t aline){
	uint16_t i;
	// move to the line
	lcd_4884_setCursor(0,aline);
	lcd_4884_clearLine(aline);
	// total chars = 84 * 48 / 6 / 9

	for(i = 0; i < 14/*total ((height * width) - (line * column))*/ ;i++){
		if(str[i] == 0)
			break;
		lcd_4884_write(str[i]);
	}
}

///////////////////////////////////////////////
// The 7-bit ASCII character set...
const PROGMEM unsigned char charset[][5] = {
	    { 0x00, 0x00, 0x00, 0x00, 0x00 },   // sp
	    { 0x00, 0x00, 0x2f, 0x00, 0x00 },   // !
	    { 0x00, 0x07, 0x00, 0x07, 0x00 },   // "
	    { 0x14, 0x7f, 0x14, 0x7f, 0x14 },   // #
	    { 0x24, 0x2a, 0x7f, 0x2a, 0x12 },   // $
	    { 0x62, 0x64, 0x08, 0x13, 0x23 },   // %
	    { 0x36, 0x49, 0x55, 0x22, 0x50 },   // &
	    { 0x00, 0x05, 0x03, 0x00, 0x00 },   // '
	    { 0x00, 0x1c, 0x22, 0x41, 0x00 },   // (
	    { 0x00, 0x41, 0x22, 0x1c, 0x00 },   // )
	    { 0x14, 0x08, 0x3E, 0x08, 0x14 },   // *
	    { 0x08, 0x08, 0x3E, 0x08, 0x08 },   // +
	    { 0x00, 0x00, 0xA0, 0x60, 0x00 },   // ,
	    { 0x08, 0x08, 0x08, 0x08, 0x08 },   // -
	    { 0x00, 0x60, 0x60, 0x00, 0x00 },   // .
	    { 0x20, 0x10, 0x08, 0x04, 0x02 },   // /
	    { 0x3E, 0x51, 0x49, 0x45, 0x3E },   // 0
	    { 0x00, 0x42, 0x7F, 0x40, 0x00 },   // 1
	    { 0x42, 0x61, 0x51, 0x49, 0x46 },   // 2
	    { 0x21, 0x41, 0x45, 0x4B, 0x31 },   // 3
	    { 0x18, 0x14, 0x12, 0x7F, 0x10 },   // 4
	    { 0x27, 0x45, 0x45, 0x45, 0x39 },   // 5
	    { 0x3C, 0x4A, 0x49, 0x49, 0x30 },   // 6
	    { 0x01, 0x71, 0x09, 0x05, 0x03 },   // 7
	    { 0x36, 0x49, 0x49, 0x49, 0x36 },   // 8
	    { 0x06, 0x49, 0x49, 0x29, 0x1E },   // 9
	    { 0x00, 0x36, 0x36, 0x00, 0x00 },   // :
	    { 0x00, 0x56, 0x36, 0x00, 0x00 },   // ;
	    { 0x08, 0x14, 0x22, 0x41, 0x00 },   // <
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
	#define pgm_buffer_size 5
    unsigned char pgm_buffer[pgm_buffer_size];
    if (chr >= ' ') {
        // Regular ASCII characters are kept in flash to save RAM...
        memcpy_P(pgm_buffer, &charset[chr - ' '], pgm_buffer_size);
        glyph = pgm_buffer;
    } else {
    	return;
    }

    // Output one column at a time...
    // One column between characters...
    hw_lcd_4884_send(PCD8544_DATA, 0x00);
    //hw_lcd_4884_send(PCD8544_DATA, 0); // the first byte of glyph is always 0
    for (unsigned char i = 0; i < pgm_buffer_size; i++) {
        hw_lcd_4884_send(PCD8544_DATA, glyph[i]);
    }

    // Update the cursor position...
    pix_x = (pix_x + 6) % width;

    if (pix_x == 0) {
        pix_y = (pix_y + 1) % height;
    }
}
