shawnchain/aprs/TinyAPRS/bertos/drv/ow_1wire.c

/**
 * \file
 * <!--
 * This file is part of BeRTOS.
 *
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
 *  Copyright (C) 2012 Robin Gilks, Peter Dannegger, Martin Thomas
 * -->
 *
 * \brief Bit bang driver for Dallas 1-wire chips
 *
 * \author Peter Dannegger (danni(at)specs.de)
 * \author Martin Thomas (mthomas(at)rhrk.uni-kl.de)
 * \author Robin Gilks <g8ecj@gilks.org>
 *
 */

#include "ow_1wire.h"

// this pulls in the low level implementation from the hardware directory
#include "hw/hw_1wire.h"


// now follows the functions that run at the lowest level and are only referenced from within this ow_1wire driver module

/**
 * Get the state of an input pin
 *
 * \return I/O pin value
 */
INLINE uint8_t
ow_input_pin_state(void)
{
	return OW_GET_IN();
}


/**
 * Enable parasitic mode (set line high to power device)
 *
 */
INLINE void
ow_parasite_enable(void)
{
	OW_OUT_HIGH();
	OW_DIR_OUT();
}

/**
 * Disable parasitic mode
 *
 */
INLINE void
ow_parasite_disable(void)
{
	OW_DIR_IN();
#if (!OW_USE_INTERNAL_PULLUP)
	OW_OUT_LOW();
#endif
}


/**
 * Disable parasitic mode
 *
 * \return non zero = error code
 */
INLINE uint8_t
ow_reset_intern(void)
{
	uint8_t err;

	OW_OUT_LOW();
	OW_DIR_OUT();
	// pull OW-Pin low for 480us
	timer_udelay(480);

	ATOMIC(
				// set Pin as input - wait for clients to pull low
				OW_DIR_IN();
#if OW_USE_INTERNAL_PULLUP
				OW_OUT_HIGH();
#endif
				timer_udelay(64);
				// no presence detect
				err = OW_GET_IN();
				// if err!=0: nobody pulled to low, still high
		);

	// after a delay the clients should release the line
	// and input-pin gets back to high by pull-up-resistor
	timer_udelay(480 - 64);
	if (OW_GET_IN() == 0)
	{
		// short circuit, expected low but got high
		err = 1;
	}

	return err;
}


/**
 * Internal function to output a bit
 * Timing issue when using runtime-bus-selection (!OW_ONE_BUS):
 * The master should sample at the end of the 15-slot after initiating
 * the read-time-slot. The variable bus-settings need more
 * cycles than the constant ones so the delays had to be shortened 
 * to achive a 15uS overall delay 
 * Setting/clearing a bit in I/O Register needs 1 cyle in OW_ONE_BUS
 * but around 14 cyles in configureable bus (us-Delay is 4 cyles per uS)
 *
 * \param b bit to output
 * \param with_parasite_enable flag to indicate whether parasitic mode to be used
 */
INLINE uint8_t
ow_bit_io_intern(uint8_t b, uint8_t with_parasite_enable)
{
	ATOMIC(
#if OW_USE_INTERNAL_PULLUP
			OW_OUT_LOW();
#endif
			// drive bus low
			OW_DIR_OUT();
			// T_INT > 1usec accoding to timing-diagramm
			timer_udelay(2);
			if (b)
			{
				// to write "1" release bus, resistor pulls high
				OW_DIR_IN();
#if OW_USE_INTERNAL_PULLUP
				OW_OUT_HIGH();
#endif
			}

			// "Output data from the DS18B20 is valid for 15usec after the falling
			// edge that initiated the read time slot. Therefore, the master must
			// release the bus and then sample the bus state within 15ussec from
			// the start of the slot."
			timer_udelay(15 - 2 - OW_CONF_DELAYOFFSET);
			if (OW_GET_IN() == 0)
			{
				// sample at end of read-timeslot
				b = 0;
			}

			timer_udelay(60 - 15 - 2 + OW_CONF_DELAYOFFSET);
#if OW_USE_INTERNAL_PULLUP
			OW_OUT_HIGH();
#endif
			OW_DIR_IN(); 
			if (with_parasite_enable)
			{
				ow_parasite_enable();
			}
	); /* ATOMIC */

	// may be increased for longer wires
	timer_udelay(OW_RECOVERY_TIME);

	return b;
}









/* now the public interfaces */

/**
 * Reset the bus, disable parasitic mode
 *
 * \return non zero = error code
 */
uint8_t
ow_reset(void)
{
	return ow_reset_intern();
}


/**
* Check for 1-wire bus being busy
*
* \return true if busy, false if not
*/
bool
ow_busy(void)
{
	return ow_bit_io(1) ? false : true;
}

/**
 * Function to output a bit
 *
 * \param b bit to output
 * \return bit read from I/O
 */
uint8_t
ow_bit_io(uint8_t b)
{
	return ow_bit_io_intern(b & 1, 0);
}

/**
 * Function to output a byte
 *
 * \param b byte to output
 * \return byte read from I/O
 */
uint8_t
ow_byte_wr(uint8_t b)
{
	uint8_t i = 8, j;

	do
	{
		j = ow_bit_io(b & 1);
		b >>= 1;
		if (j)
		{
			b |= 0x80;
		}
	}
	while (--i);

	return b;
}

/**
 * Function to output a byte in parasitic mode
 *
 * \param b byte to output
 * \return byte read from I/O
 */
uint8_t
ow_byte_wr_with_parasite_enable(uint8_t b)
{
	uint8_t i = 8, j;

	do
	{
		if (i != 1)
		{
			j = ow_bit_io_intern(b & 1, 0);
		}
		else
		{
			j = ow_bit_io_intern(b & 1, 1);
		}
		b >>= 1;
		if (j)
		{
			b |= 0x80;
		}
	}
	while (--i);

	return b;
}


/**
 * Function to read a byte
 *
 * \return byte read from I/O
 */
uint8_t
ow_byte_rd(void)
{
	// read by sending only "1"s, so bus gets released
	// after the init low-pulse in every slot
	return ow_byte_wr(0xFF);
}


/**
 * Function to implement ROM search algorithm
 *
 * \param diff Where to start in the search path
 * \param id pointer to 8 octet id buffer
 * \return next search path dirction
 */
uint8_t
ow_rom_search(uint8_t diff, uint8_t * id)
{
	uint8_t i, j, next_diff;
	uint8_t b;

	if (ow_reset())
	{
		// error, no device found <--- early exit!
		return OW_PRESENCE_ERR;
	}

	ow_byte_wr(OW_SEARCH_ROM);
	// unchanged on last device
	next_diff = OW_LAST_DEVICE;

	// number of bits in romcode
	i = OW_ROMCODE_SIZE * 8;

	do
	{
		// 8 bits
		j = 8;
		do
		{
			// read bit
			b = ow_bit_io(1);
			if (ow_bit_io(1))
			{
				// read complement bit
				if (b)
				{
					// bit pattern 0b11 - data error <--- early exit!
					return OW_DATA_ERR;
				}
			}
			else
			{
				// 0b00 = 2 devices
				if (!b)
				{
					if (diff > i || ((*id & 1) && diff != i))
					{
						b = 1;
						next_diff = i;
					}
				}
			}
			// write bit
			ow_bit_io(b);
			*id >>= 1;
			if (b)
			{
				// store bit
				*id |= 0x80;
			}

			i--;

		}
		while (--j);

		// next byte of ID
		id++;

	}
	while (i);

	// to continue search
	return next_diff;
}


/**
 * Internal function to output a command to a device
 *
 * \param command byte to output to device
 * \param id pointer to 8 octet id buffer of device to send to
 * \param with_parasite_enable flag to indicate whether parasitic mode to be used
 */
static void
ow_command_intern(uint8_t command, uint8_t * id, uint8_t with_parasite_enable)
{
	uint8_t i;

	ow_reset();

	if (id)
	{
		// to a single device
		ow_byte_wr(OW_MATCH_ROM);
		i = OW_ROMCODE_SIZE;
		do
		{
			ow_byte_wr(*id);
			id++;
		}
		while (--i);
	}
	else
	{
		// to all devices
		ow_byte_wr(OW_SKIP_ROM);
	}

	if (with_parasite_enable)
	{
		ow_byte_wr_with_parasite_enable(command);
	}
	else
	{
		ow_byte_wr(command);
	}
}

/**
 * Function to output a command to a device
 *
 * \param command byte to output to device
 * \param id pointer to 8 octet id buffer of device to send to
 */
void
ow_command(uint8_t command, uint8_t * id)
{
	ow_command_intern(command, id, 0);
}

/**
 * Function to output a command to a device in parasitic mode
 *
 * \param command byte to output to device
 * \param id pointer to 8 octet id buffer of device to send to
 */
void
ow_command_with_parasite_enable(uint8_t command, uint8_t * id)
{
	ow_command_intern(command, id, 1);
}

/**
 * Function to output a block of data to a device
 * Device must have been previously selected with a 'command'
 *
 * \param buff buffer to output to device
 * \param len length of data to send
 */
void
ow_block(uint8_t * buff, uint8_t len)
{
	uint8_t i;

	for (i = 0; i < len; i++)
		buff[i] = ow_byte_wr(buff[i]);

}
