shawnchain/aprs/TinyAPRS/TinyAPRS/gps.h

/*
 * \file gps.h
 * <!--
 * This file is part of TinyAPRS.
 * Released under GPL License
 *
 * Copyright 2015 Shawn Chain (shawn.chain@gmail.com)
 *
 * -->
 *
 * \brief 
 *
 * \author shawn
 * \date 2015-3-27
 */

/*
  nmea.cpp - NMEA 0183 sentence decoding library for Wiring & Arduino
  Copyright (c) 2008 Maarten Lamers, The Netherlands.
  All right reserved.

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
  You should have received a copy of the GNU Lesser General Public
  License along with this library; if not, write to the Free Software
  Foundation, Inc., 51 Franklin St, Fifth Floor, Boston, MA  02110-1301  USA
*/

#ifndef NMEA_H_
#define NMEA_H_

#include "cfg/cfg_gps.h"
#include <stdio.h>
#include <stdbool.h>

#define	ALL					0						// connect to all datatypes
#define	GPRMC				1						// connect only to GPRMC datatype
#define	MTR					1.0						// meters per meter
#define	KM					0.001					// kilometers per meter
#define	MI					0.00062137112			// miles per meter
#define	NM					0.00053995680			// nautical miles per meter
#define	PARSEC				0.000000000000			// parsecs per meter (approximation)
#define	MPS					0.51444444 				// meters-per-second in one knot
#define	KMPH				1.852f  				// kilometers-per-hour in one knot
#define	MPH					1.1507794				// miles-per-hour in one knot
#define	KTS					1.0 					// knots in one knot
#define	LIGHTSPEED			0.000000001716			// lightspeeds in one knot

#define MAX_TERMS 			16
#define MAX_SENTENCEN_CHARS 80
#define MIN_SENTENCEN_CHARS 7

#define GPRMC_TERM_UTC_TIME 0
#define GPRMC_TERM_STATUS 1
#define GPRMC_TERM_LATITUDE 2
#define GPRMC_TERM_LATITUDE_NS 3
#define GPRMC_TERM_LONGITUDE 4
#define GPRMC_TERM_LONGITUDE_WE 5
#define GPRMC_TERM_SPEED 6
#define GPRMC_TERM_HEADING 7
#define GPRMC_TERM_DATE 8

#define GPGGA_TERM_FIXQUALITY 5
#define GPGGA_TERM_ALTITUDE 8


typedef void (*gps_callback)(void*);

typedef struct GPS{
	bool	valid;
	char*	_term[MAX_TERMS];
	uint16_t altitude;	// altitude value reads from GPGGA[8]
}GPS;

typedef struct Location{
	float latitude; 	// decimal(xx.xx) degrees of latitude
	float longitude;
	float speedInKMH;
	uint16_t heading;
	uint16_t altitude;	// altitude value reads from GPGGA[8]
	uint32_t timestamp;
}Location;

/*
 *
 */
void gps_init(GPS *gps);


int gps_parse(GPS *gps, char *sentence, size_t len);

void gps_get_location(GPS *gps, Location *pLoc);

float nmea_decimal_float(char* s);

uint16_t nmea_decimal_int(char* s);

float gps_distance_between(Location *loc1, Location *loc2, float units_per_meter) ;
/*
 * FIXME temporary solution for GPS signal indicator
 */
#define GPS_LED_INIT() do { DDRB |= BV(5);/*PIN13, PIN10*/ } while (0)
#define GPS_LED_ON()   do { PORTB |= BV(5); } while (0) // PIN9
#define GPS_LED_OFF()  do { PORTB &= ~BV(5); } while (0)
#endif /* NMEA_H_ */
