shawnchain/aprs/TinyAPRS/bertos/drv/ow_ds2438.h

/**
 * \file
 * <!--
 * This file is part of BeRTOS.
 *
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
 *  Copyright (C) 2012 Robin Gilks
 * -->
 *
 * \addtogroup ow_driver 1-wire driver
 * \ingroup drivers
 * \{
 *
 * \brief Driver for Dallas battery monitor 1-wire device
 *
 * \author Robin Gilks <g8ecj@gilks.org>
 * $WIZ$ module_name = "ow_ds2438"
 * $WIZ$ module_depends = "1wire", "crc8"
 */

#ifndef OW_DS2438_H_
#define OW_DS2438_H_


#include <stdint.h>

#include "drv/ow_1wire.h"


#define SBATTERY_FAM  0x26

#define CONF2438_IAD  0x01
#define CONF2438_CA   0x02
#define CONF2438_EE   0x04
#define CONF2438_AD   0x08
#define CONF2438_TB   0x10
#define CONF2438_NVB  0x20
#define CONF2438_ADB  0x40
#define CONF2438_ALL  0x7f


	/**
	 * \defgroup battery_api DS2438 API
	 * With this driver you can read the parameters of a DS2438 battery monitor chip.
	 * You can initialise the module to sync the charge value to that with the actual battery.
	 *
	 * API usage example:
	 * \code
	 * static CTX2438_t BatteryCtx;   // declare a context structure
	 * ow_ds2438_init (ids[battid], &BatteryCtx, RSHUNT, CHARGE);  set the current charge state of the battery and the value of the shunt resistor
	 * ow_ds2438_doconvert (ids[battid]);          // do the current and temperature conversions
	 * if (!ow_ds2438_readall (ids[battid], &BatteryCtx))
	 * BatteryCtx.Temp BatteryCtx.Volts BatteryCtx.Amps BatteryCtx.Charge etc contain the values requested
	 * \endcode
	 * \{
	 */

/**
 * Results from reading everything from a DS2438 chip, also tracks charge accumulator on a particular chip
 */

typedef struct 
{
	int16_t Temp;           ///< Temperature
	uint16_t Volts;         ///< Voltage on Vdd or Vad pin
	int16_t Amps;           ///< Current, depends on external shunt to interpret the actual value
	uint16_t Charge;        ///< Charge value in amp-hrs
	uint16_t CCA;           ///< Charging Current Accumulator
	uint16_t DCA;           ///< Discharge Current Accumulator
// internal variables
	uint32_t fullICA;       ///< internal representation of value read expanded to 32 bits - scaled by 100
	uint8_t lastICA;        ///< last value read from the chip
	float shunt;            ///< value of the shunt resistor used to measure current and charge
	uint32_t etm;           ///< elapsed timer meter
} CTX2438_t;

int ow_ds2438_init(uint8_t id[], CTX2438_t * context, float shunt, uint16_t charge);
int ow_ds2438_setup(uint8_t id[], int config);
void ow_ds2438_doconvert(uint8_t id[]);
int ow_ds2438_readall(uint8_t id[], CTX2438_t * context);
int ow_ds2438_calibrate(uint8_t id[], CTX2438_t * context, int16_t offset);
int ow_ds2438_setCCADCA(uint8_t id[], CTX2438_t * context);
int ow_ds2438_setETM(uint8_t id[], uint32_t etm);
	/** \} */ //defgroup battery_api

/** \} */ //addtogroup ow_driver

#endif
