shawnchain/aprs/TinyAPRS/bertos/cfg/cfg_1wire.h

/**
 * \file
 * <!--
 * This file is part of BeRTOS.
 *
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
 *  Copyright (C) 2012 Robin Gilks, Peter Dannegger, Martin Thomas
 * -->
 *
 * \brief Configuration file for 1 wire bus
 *
 * \author Peter Dannegger (danni(at)specs.de)
 * \author Martin Thomas (mthomas(at)rhrk.uni-kl.de)
 * \author Robin Gilks (g8ecj(at)gilks.org)
 * \author Francesco Sacchi <asterix@develer.com>
 */

#ifndef CFG_1WIRE_H
#define CFG_1WIRE_H

/**
 * Module logging level.
 *
 * $WIZ$ type = "enum"
 * $WIZ$ value_list = "log_level"
 */
#define OW_LOG_LEVEL      LOG_LVL_WARN

/**
 * Module logging format.
 *
 * $WIZ$ type = "enum"
 * $WIZ$ value_list = "log_format"
 */
#define OW_LOG_FORMAT     LOG_FMT_TERSE

/**
 * One bus for 1-wire devices
 *
 * $WIZ$ type = "boolean"
 */
#define OW_ONE_BUS   0


/**
 * Use internal pullup
 *
 * $WIZ$ type = "boolean"
 */
// Use AVR's internal pull-up resistor instead of external 4,7k resistor.
// Based on information from Sascha Schade. Experimental but worked in tests
// with one DS18B20 and one DS18S20 on a rather short bus (60cm), where both 
// sensores have been parasite-powered.
#define OW_USE_INTERNAL_PULLUP     1    /* 0=external, 1=internal */

/**
 *  1-wire data direction port.
 *
 * $WIZ$ type = "enum"
 * $WIZ$ value_list = "onewire_ddr_list"
 */
#if OW_ONE_BUS == 1
#define OW_DDR  DDRB
#endif

/**
 *  1-wire data pin
 *
 * $WIZ$ type = "enum"
 * $WIZ$ value_list = "onewire_pin_list"
 */
#if OW_ONE_BUS == 1
#define OW_PIN  PB0
#endif


/**
 *  1-wire input port
 *
 * $WIZ$ type = "enum"
 * $WIZ$ value_list = "onewire_portin_list"
 */
#if OW_ONE_BUS == 1
#define OW_IN   PINB
#endif

/**
 *  1-wire output port
 *
 * $WIZ$ type = "enum"
 * $WIZ$ value_list = "onewire_portout_list"
 */
#if OW_ONE_BUS == 1
#define OW_OUT  PORTB
#endif


/**
 * Recovery time (T_Rec) minimum 1usec - increase for long lines 
 * 5 usecs is a value give in some Maxim AppNotes
 * 30u secs seem to be reliable for longer lines
 *
 * $WIZ$ type = "int"; min = 1; max = 50
 */
#define OW_RECOVERY_TIME         10



#endif /* CFG_1WIRE_H */
