shawnchain/aprs/TinyAPRS/TinyAPRS/beacon.h

/*
 * \file beacon.h
 * <!--
 * This file is part of TinyAPRS.
 * Released under GPL License
 *
 * Copyright 2015 Shawn Chain (shawn.chain@gmail.com)
 *
 * -->
 *
 * \brief 
 *
 * \author shawn
 * \date 2015-2-13
 */

#ifndef BEACON_H_
#define BEACON_H_

#include "cfg/cfg_beacon.h"

#include <stdbool.h>

// Beacon module callback
typedef void (*beacon_exit_callback_t)(void);

/*
 * Initialize the beacon module
 */
void beacon_init(beacon_exit_callback_t exitcb);

/*
 * Runloop of the beacon module
 */
void beacon_broadcast_poll(void);

/*
 * Send raw payload
 */
void beacon_send(char* payload, uint8_t payloadLen);

#if CFG_BEACON_TEST
/*
 * Send the beacon test message payload
 */
void beacon_send_test_message_immediate(uint8_t repeats, const char* text);
#endif

#endif /* BEACON_H_ */
